zambujal/CPLD-XC95288XL-replacement-for-scld-timex/docs/images/image-1777061562731.jpg

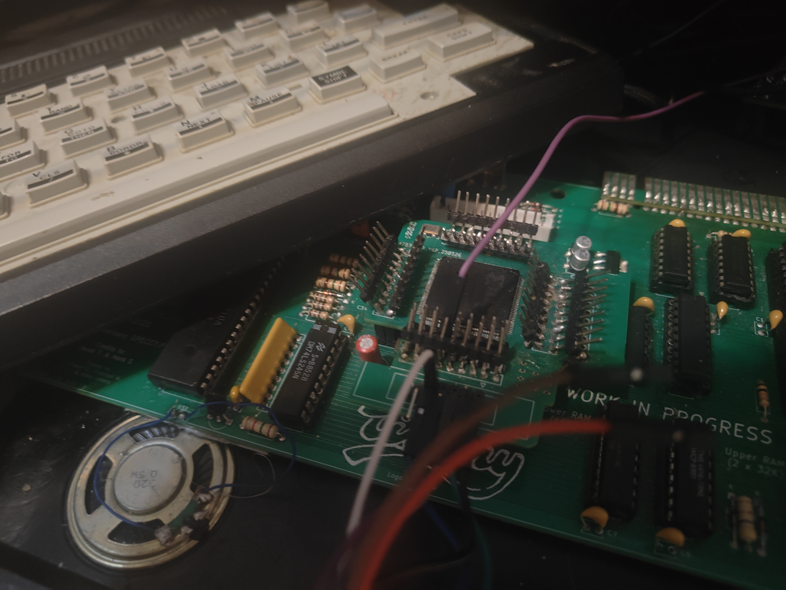
docs/images/image-1777061562731.jpg
