zambujal/CPLD-XC95288XL-replacement-for-scld-timex/docs/images/image-1777061581313.jpg

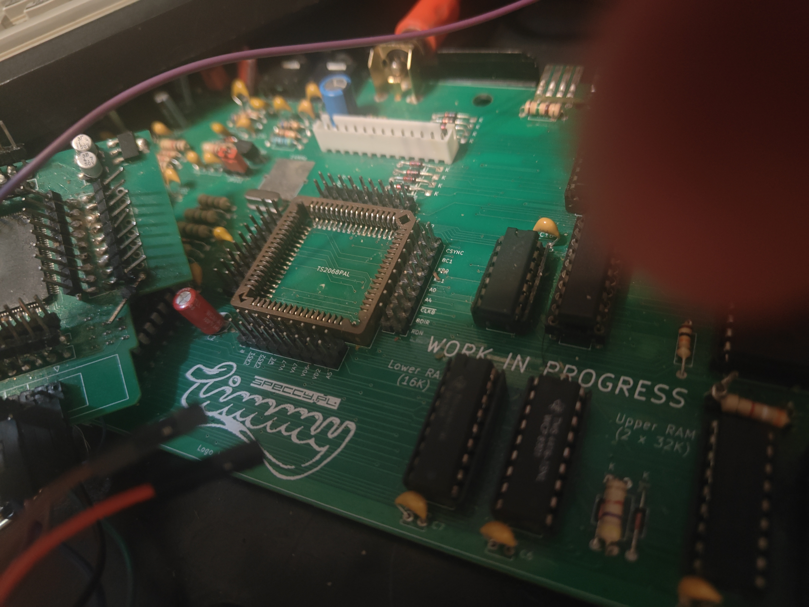
docs/images/image-1777061581313.jpg
