zambujal/CPLD-XC95288XL-replacement-for-scld-timex/docs/images/IMG20260424214503.jpg

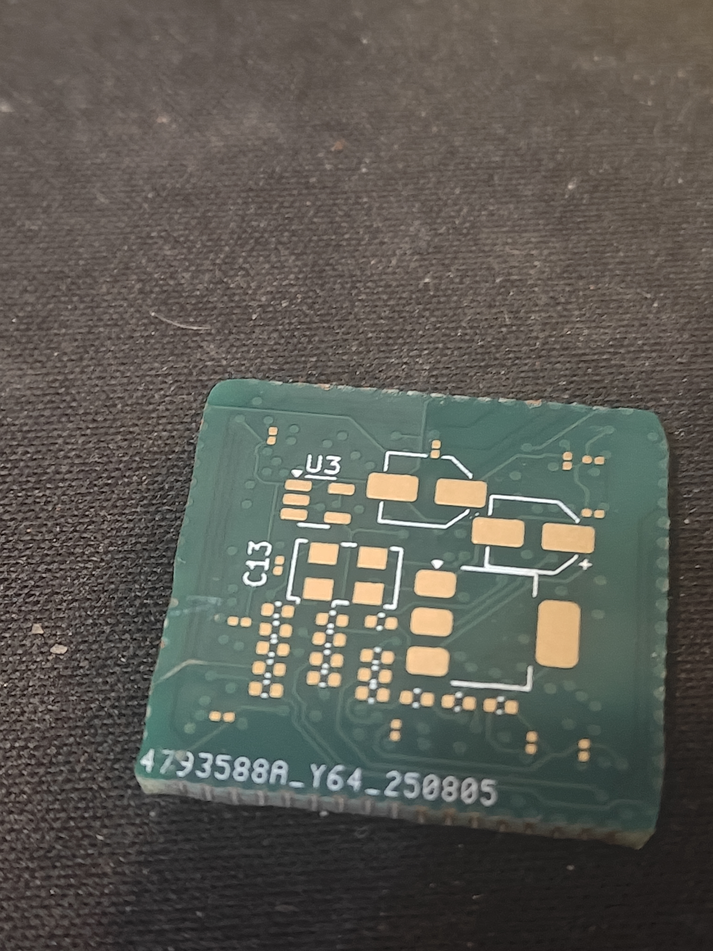
docs/images/IMG20260424214503.jpg
