zambujal/CPLD-XC95288XL-replacement-for-scld-timex/Hardware/Schematics/288 cpld alpha.kicad_sch

## KiCad design Hardware/Schematics/288 cpld alpha.kicad_sch (2026-04-24)

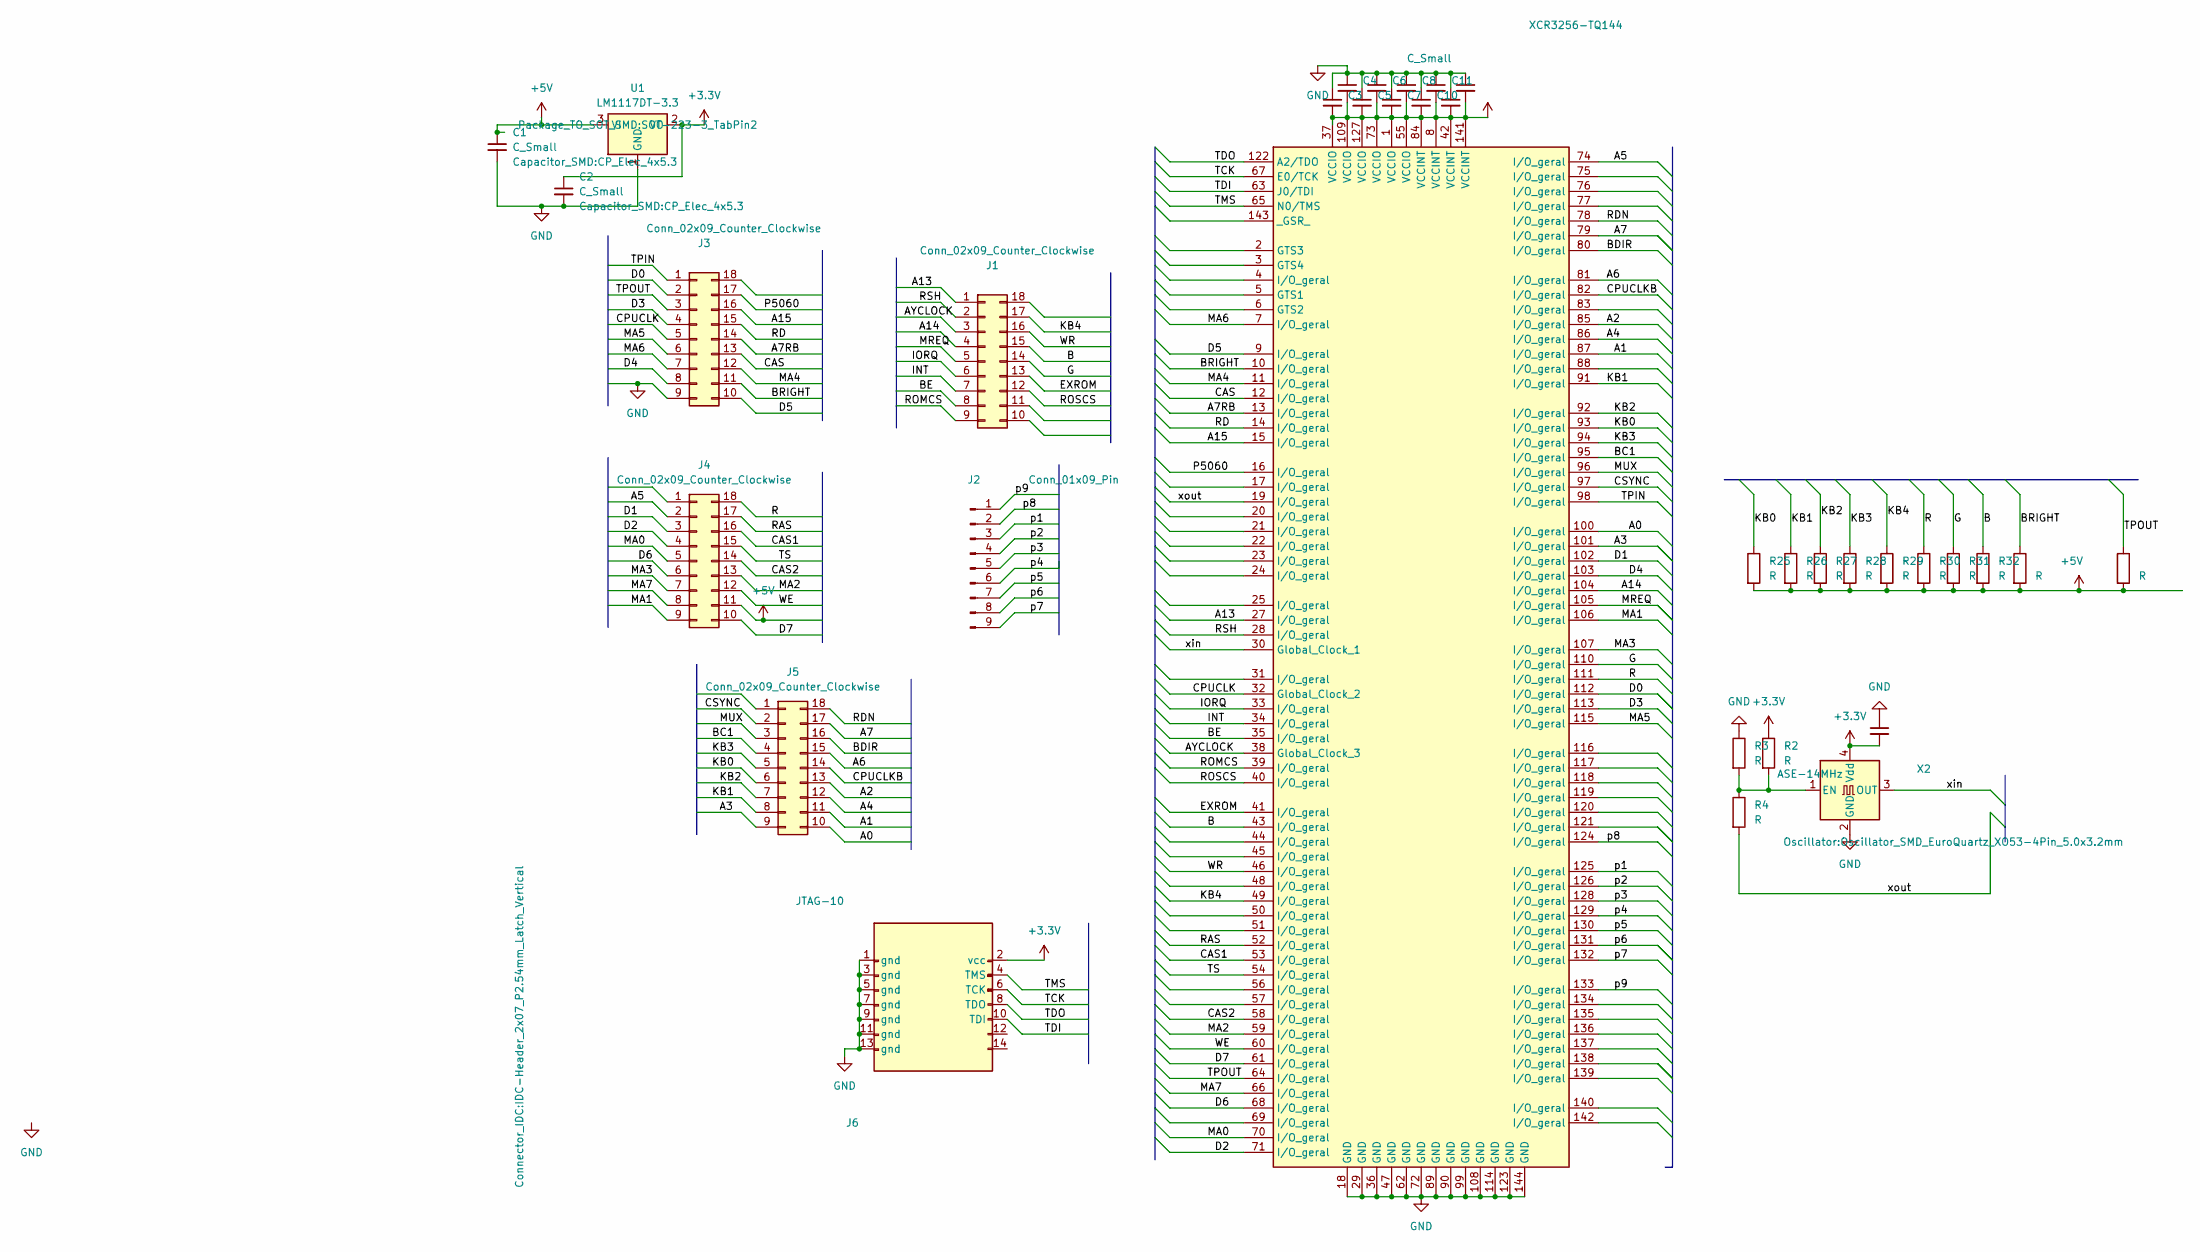
[picture p17: schematic 288 cpld alpha.kicad_sch]

Parts:
C1, C2: C_Small; CP_Elec_4x5.3
C3, C4, C5, C6, C7, C8, C9, C10, C11, C12, C13: C_Small; C_0201_0603Metric
J1, J3, J4, J5: Conn_02x09_Counter_Clockwise; PinHeader_2x09_P2.54mm_Vertical
J2: Conn_01x09_Pin; PinHeader_1x09_P2.54mm_Vertical
J6: JTAG-10; IDC-Header_2x07_P2.54mm_Latch_Vertical
R1, R2, R3, R4, R25, R26, R27, R28, R29, R30, R31, R32, R33: R; R_0402_1005Metric
U1: LM1117DT-3.3; SOT-223-3_TabPin2
U2: XCR3256-TQ144; TQFP-144_20x20mm_P0.5mm
X2: ASE-14MHz; Oscillator_SMD_EuroQuartz_XO53-4Pin_5.0x3.2mm

Connections:
+3.3V: C2.1, C3.2, C4.2, C5.2, C6.2, C7.2, C8.2, C9.2, C10.2, C11.2, C12.2, C13.2, J6.2 (vcc), R2.1, U1.2 (VO), U2.1 (VCCIO), U2.8 (VCCINT), U2.37 (VCCIO), U2.42 (VCCINT), U2.55 (VCCIO), U2.73 (VCCIO), U2.84 (VCCINT), U2.109 (VCCIO), U2.127 (VCCIO), U2.141 (VCCINT), X2.4 (Vdd)
+5V: C1.1, R1.2, R25.2, R26.2, R27.2, R28.2, R29.2, R30.2, R31.2, R32.2, R33.2, U1.3 (VI)
A0: U2.100 (I/O_geral)
A1: U2.87 (I/O_geral)
A2: U2.85 (I/O_geral)
A3: U2.101 (I/O_geral)
A4: U2.86 (I/O_geral)
A5: U2.74 (I/O_geral)
A6: U2.81 (I/O_geral)
A7: U2.79 (I/O_geral)
A7RB: U2.13 (I/O_geral)
A13: U2.27 (I/O_geral)
A14: U2.104 (I/O_geral)
A15: U2.15 (I/O_geral)
AYCLOCK: U2.38 (Global_Clock_3)
B: R32.1, U2.43 (I/O_geral)
BC1: U2.95 (I/O_geral)
BDIR: U2.80 (I/O_geral)
BE: U2.35 (I/O_geral)
BRIGHT: R33.1, U2.10 (I/O_geral)
CAS: U2.12 (I/O_geral)
CAS1: U2.53 (I/O_geral)
CAS2: U2.58 (I/O_geral)
CPUCLK: U2.32 (Global_Clock_2)
CPUCLKB: U2.82 (I/O_geral)
CSYNC: U2.97 (I/O_geral)
D0: U2.112 (I/O_geral)
D1: U2.102 (I/O_geral)
D2: U2.71 (I/O_geral)
D3: U2.113 (I/O_geral)
D4: U2.103 (I/O_geral)
D5: U2.9 (I/O_geral)
D6: U2.68 (I/O_geral)
D7: U2.61 (I/O_geral)
EXROM: U2.41 (I/O_geral)
G: R31.1, U2.110 (I/O_geral)
GND: C1.2, C2.2, C3.1, C4.1, C5.1, C6.1, C7.1, C8.1, C9.1, C10.1, C11.1, C12.1, C13.1, J6.1 (gnd), J6.3 (gnd), J6.5 (gnd), J6.7 (gnd), J6.9 (gnd), J6.11 (gnd), J6.13 (gnd), R3.1, U1.1 (GND), U2.18 (GND), U2.29 (GND), U2.36 (GND), U2.47 (GND), U2.62 (GND), U2.72 (GND), U2.89 (GND), U2.90 (GND), U2.99 (GND), U2.108 (GND), U2.114 (GND), U2.123 (GND), U2.144 (GND), X2.2 (GND)
INT: U2.34 (I/O_geral)
IORQ: U2.33 (I/O_geral)
KB0: R25.1, U2.93 (I/O_geral)
KB1: R26.1, U2.91 (I/O_geral)
KB2: R27.1, U2.92 (I/O_geral)
KB3: R28.1, U2.94 (I/O_geral)
KB4: R29.1, U2.49 (I/O_geral)
MA0: U2.70 (I/O_geral)
MA1: U2.106 (I/O_geral)
MA2: U2.59 (I/O_geral)
MA3: U2.107 (I/O_geral)
MA4: U2.11 (I/O_geral)
MA5: U2.115 (I/O_geral)
MA6: U2.7 (I/O_geral)
MA7: U2.66 (I/O_geral)
MREQ: U2.105 (I/O_geral)
MUX: U2.96 (I/O_geral)
unnamed: R2.2, R3.2, R4.1, X2.1 (EN)
P5060: U2.16 (I/O_geral)
R: R30.1, U2.111 (I/O_geral)
RAS: U2.52 (I/O_geral)
RD: U2.14 (I/O_geral)
RDN: U2.78 (I/O_geral)
ROMCS: U2.39 (I/O_geral)
ROSCS: U2.40 (I/O_geral)
RSH: U2.28 (I/O_geral)
TCK: U2.67 (E0/TCK)
TDI: U2.63 (J0/TDI)
TDO: U2.122 (A2/TDO)
TMS: U2.65 (N0/TMS)
TPIN: U2.98 (I/O_geral)
TPOUT: R1.1, U2.64 (I/O_geral)
TS: U2.54 (I/O_geral)
WE: U2.60 (I/O_geral)
WR: U2.46 (I/O_geral)
p1: U2.125 (I/O_geral)
p2: U2.126 (I/O_geral)
p3: U2.128 (I/O_geral)
p4: U2.129 (I/O_geral)
p5: U2.130 (I/O_geral)
p6: U2.131 (I/O_geral)
p7: U2.132 (I/O_geral)
p8: U2.124 (I/O_geral)
p9: U2.133 (I/O_geral)
xin: U2.30 (Global_Clock_1), X2.3 (OUT)
xout: R4.2, U2.19 (I/O_geral)
